Jaycar-Electronics/Uno-Clock/other/20151216_122853.jpg

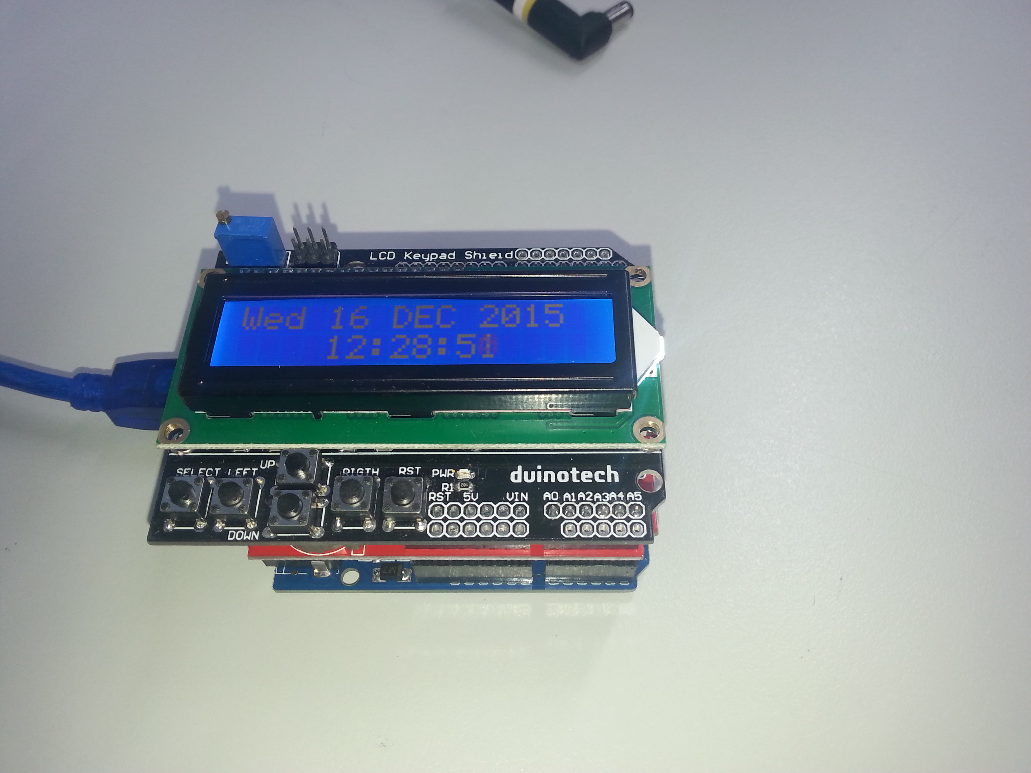
other/20151216_122853.jpg
